DianxinWang/Final-Design/version 2.0/shaft/shaft_side.SLDASM

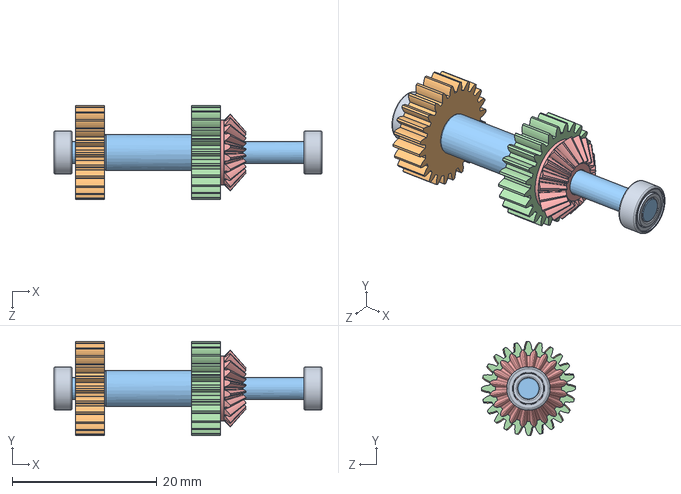
[picture p52: CAD file, 2018-03-30]
version 2.0/shaft/shaft_side.SLDASM
37.0 x 13.0 x 13.0 mm
bearing 3-6-2.5 x 2
shaft_side
