DianxinWang/Final-Design/version 2.0/motor/motor_10_1.SLDASM

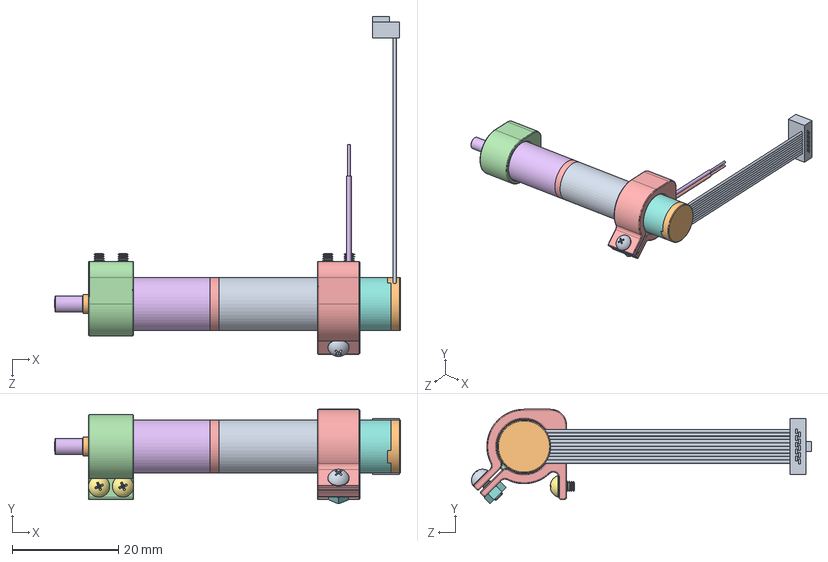
[picture p53: CAD file, 2018-03-30]
version 2.0/motor/motor_10_1.SLDASM
65.1 x 17.8 x 63.9 mm
motor_base-10_11
motor_base-10_22
motor_10_transfer
screw_shi M2X3 x 4
nut M2
screw_shi M2X5
