DianxinWang/Final-Design/version 2.0/shaft/shaft_side_1.SLDASM

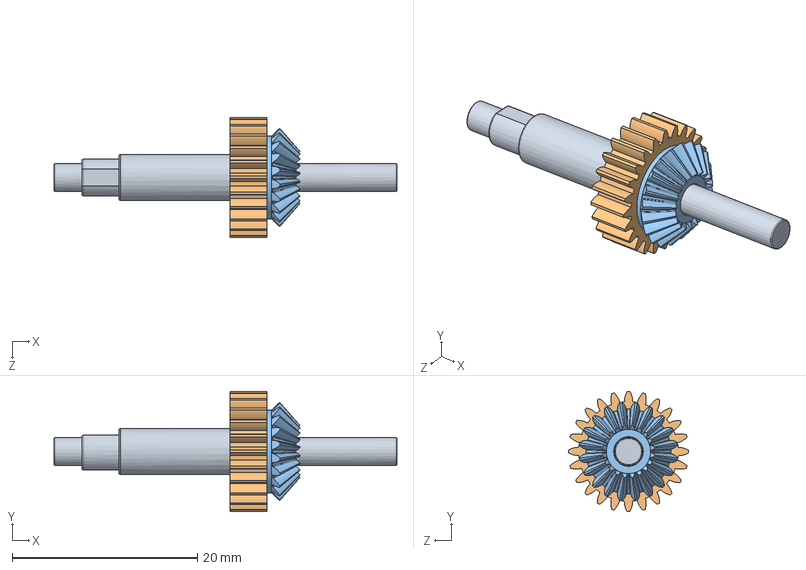
[picture p54: CAD file, 2018-03-30]
version 2.0/shaft/shaft_side_1.SLDASM
37.0 x 13.0 x 13.0 mm
shaft_side
GB - Spur gear 0.5M 24T 20PA 4FW
GB - Straight bevel pinion 0.5M20PT 20GT 20PA 3.3FW
