DianxinWang/Final-Design/version 2.0/motor/motor_10/maxon_dcx10.SLDASM

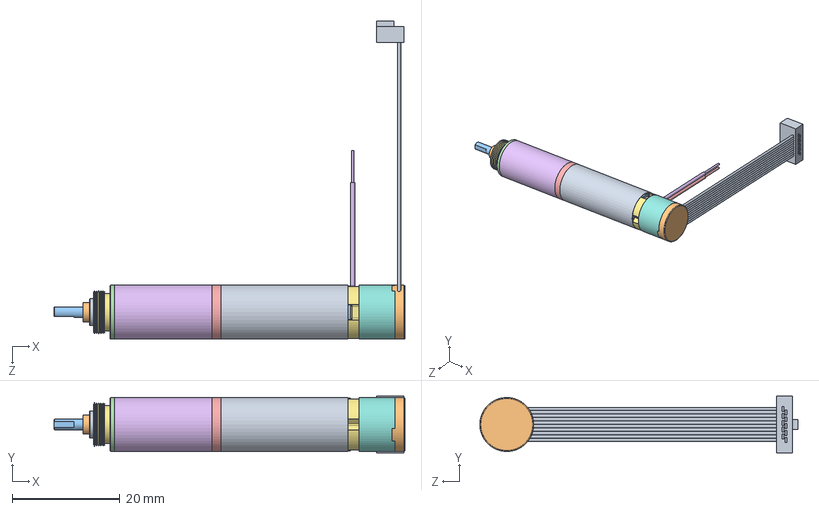
[picture p55: CAD file, 2018-03-30]
version 2.0/motor/motor_10/maxon_dcx10.SLDASM
65.1 x 10.5 x 59.0 mm
