DianxinWang/Final-Design/version 2.0/Index/index-1-1.SLDPRT

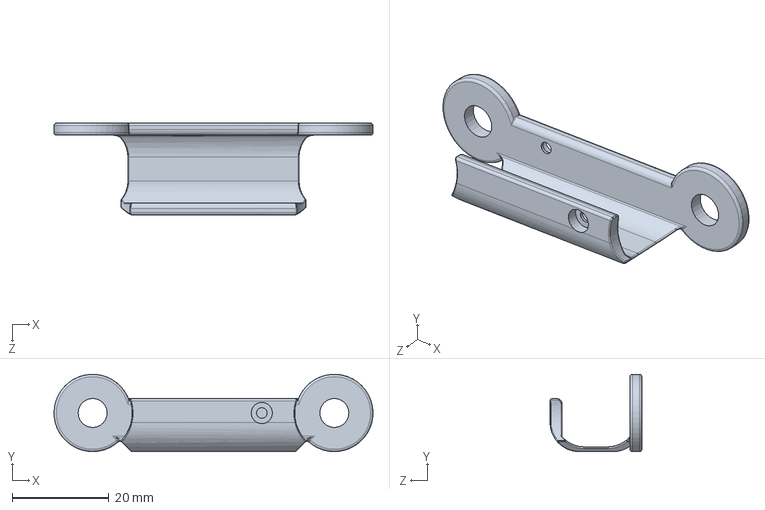
[picture p56: CAD file, 2018-03-30]
version 2.0/Index/index-1-1.SLDPRT
66.0 x 16.0 x 19.0 mm
