DianxinWang/Final-Design/version 2.0/little_finger/little_finger-2.SLDPRT

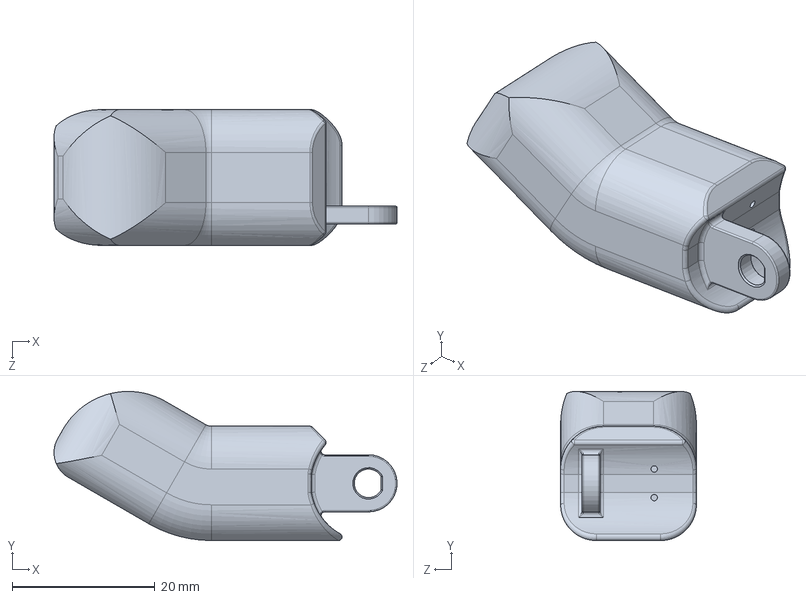
[picture p57: CAD file, 2018-03-30]
version 2.0/little_finger/little_finger-2.SLDPRT
48.0 x 20.9 x 19.0 mm
