DianxinWang/Final-Design/version 2.0/middle_finger/middle_finger-1-2.SLDPRT

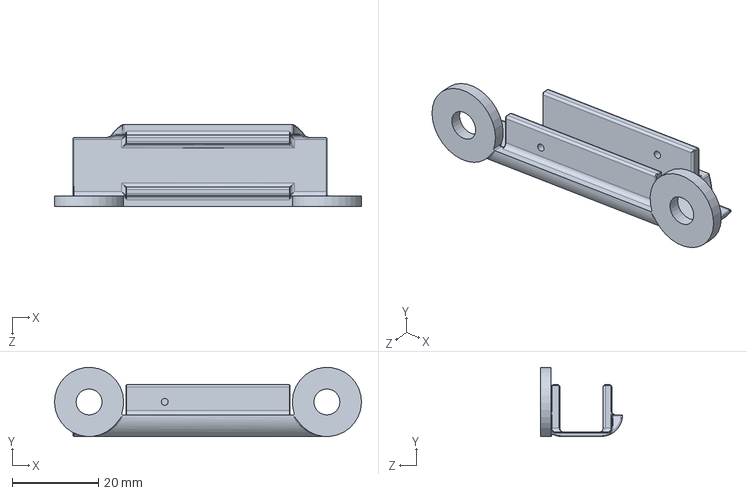
[picture p58: CAD file, 2018-03-30]
version 2.0/middle_finger/middle_finger-1-2.SLDPRT
71.0 x 16.0 x 19.0 mm
