DianxinWang/Final-Design/version 2.0/motor/f-motor-base/motor_base-11.SLDPRT

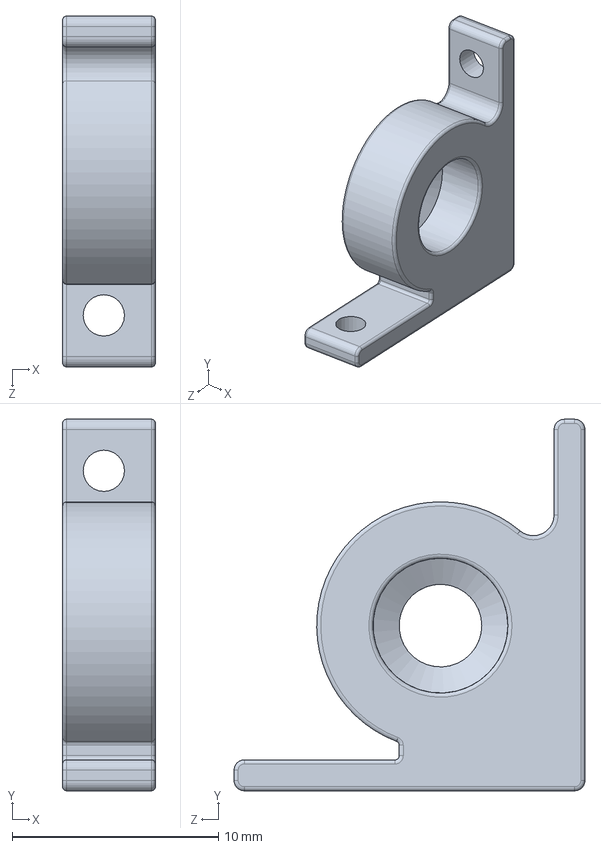
[picture p59: CAD file, 2018-03-30]
version 2.0/motor/f-motor-base/motor_base-11.SLDPRT
4.50 x 18.0 x 17.0 mm
