DianxinWang/Final-Design/version 2.0/motor/motor_10/Gear.sldprt

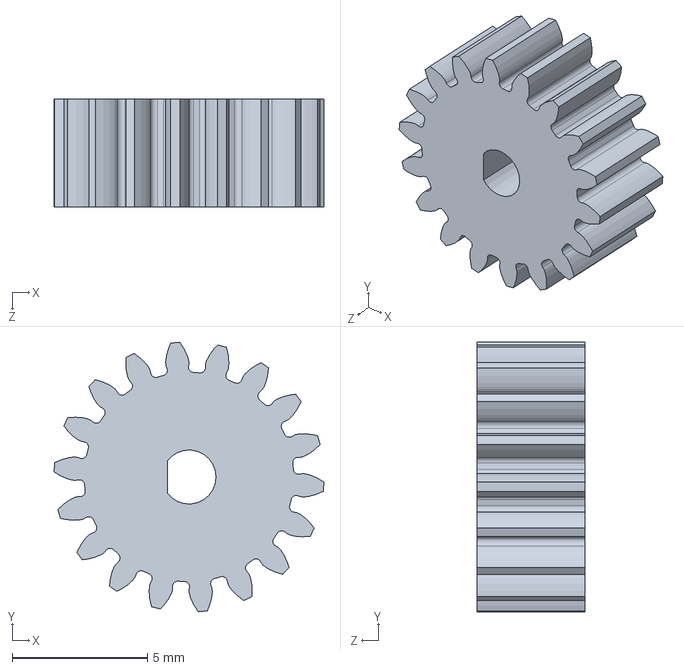
[picture p60: CAD file, 2018-03-30]
version 2.0/motor/motor_10/Gear.sldprt
9.99 x 9.98 x 4.00 mm
