DianxinWang/Final-Design/version 2.0/motor/motor_base-10_2.SLDPRT

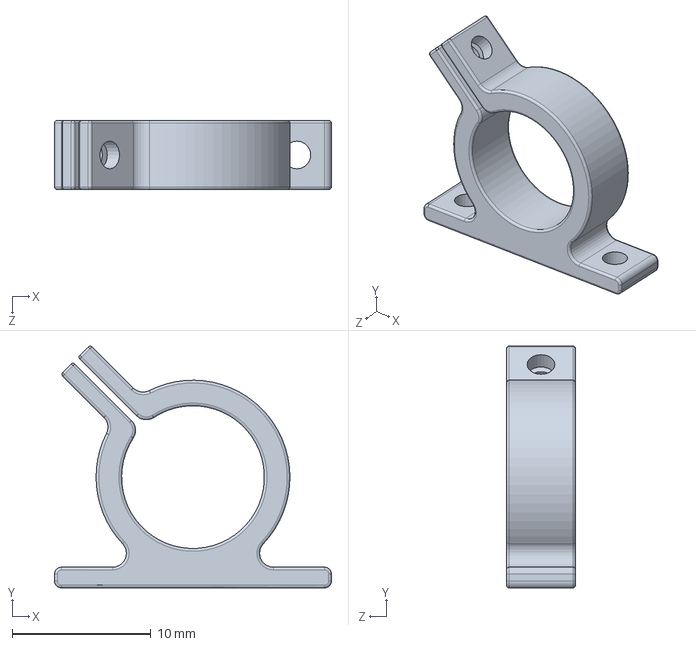
[picture p61: CAD file, 2018-03-30]
version 2.0/motor/motor_base-10_2.SLDPRT
20.0 x 17.5 x 5.00 mm
