DianxinWang/Final-Design/version 2.0/palm/bearing_base_1.SLDPRT

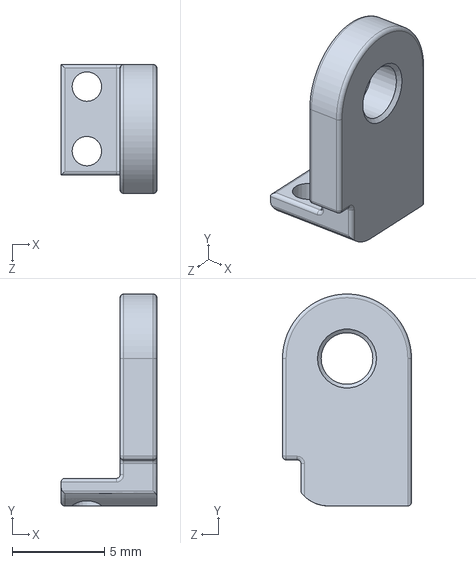
[picture p62: CAD file, 2018-03-30]
version 2.0/palm/bearing_base_1.SLDPRT
5.20 x 11.5 x 7.00 mm
