DianxinWang/Final-Design/version 2.0/传动件图纸/5-gear 0.5M 24T 4FW & pulley 2GT-16 5FW（有修改）.STEP

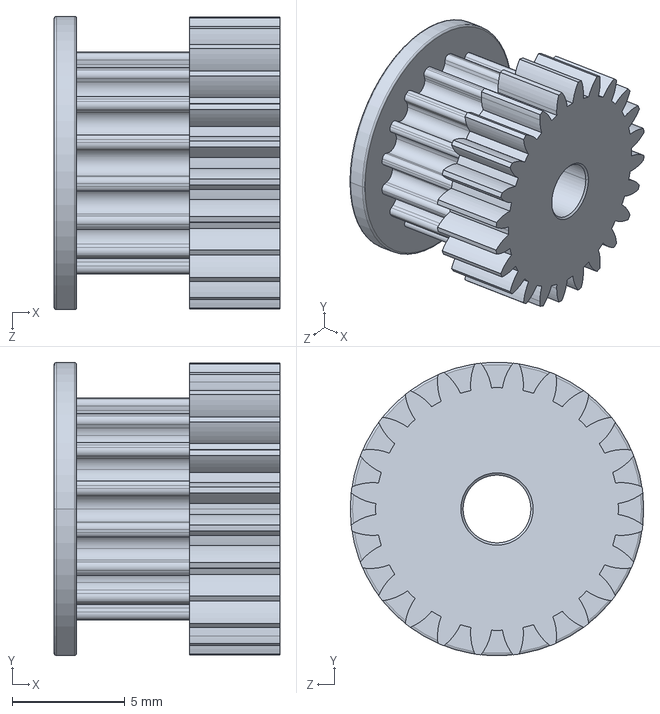
[picture p63: CAD file, 2018-03-30]
version 2.0/传动件图纸/5-gear 0.5M 24T 4FW & pulley 2GT-16 5FW（有修改）.STEP
10.0 x 13.0 x 13.0 mm
