DianxinWang/Final-Design/version 2.0/标准件/bearing 2-5-2.3.sldprt

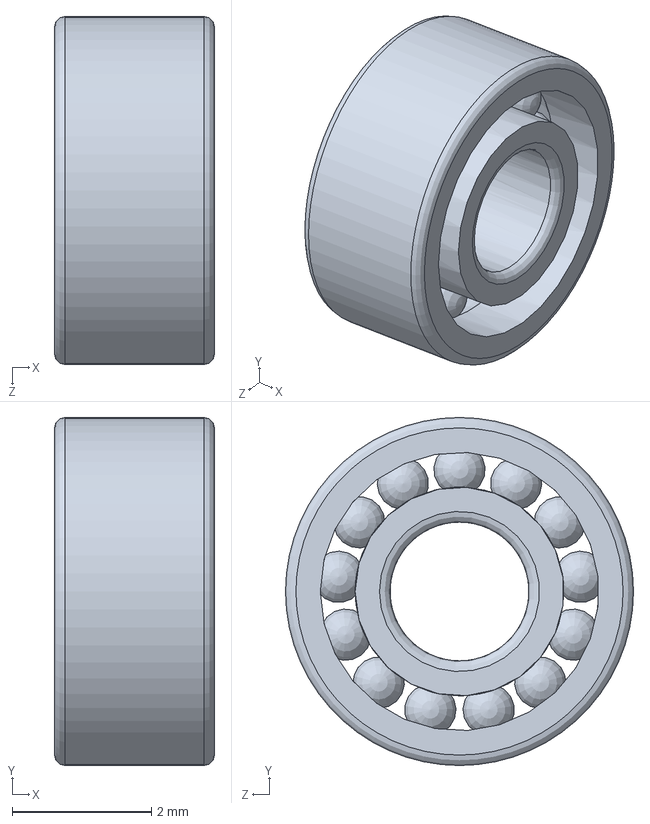
[picture p64: CAD file, 2018-03-30]
version 2.0/标准件/bearing 2-5-2.3.sldprt
2.30 x 5.00 x 5.00 mm
