DianxinWang/Final-Design/version 2.0/标准件/waste/gear 0.5M 24T 4.5FW-pulley 2GT-162.SLDPRT

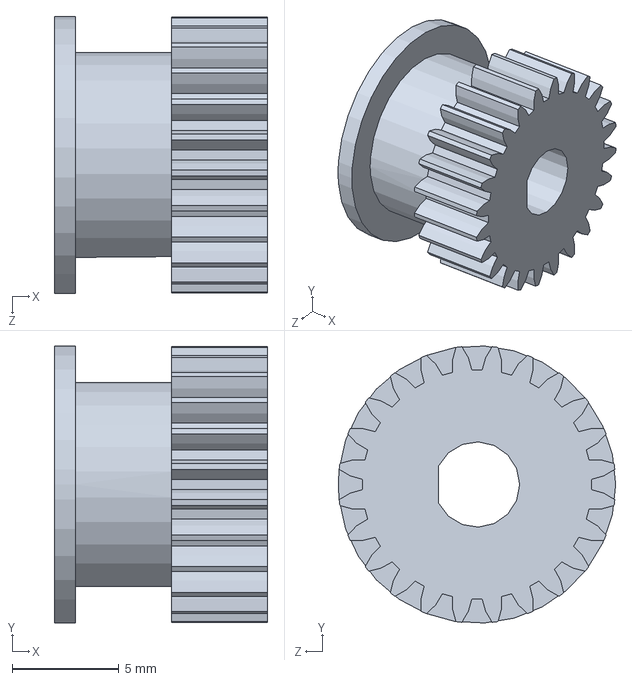
[picture p65: CAD file, 2018-03-30]
version 2.0/标准件/waste/gear 0.5M 24T 4.5FW-pulley 2GT-162.SLDPRT
10.0 x 13.0 x 13.0 mm
