DianxinWang/Final-Design/version 2.0/Index/index-1-2.SLDPRT

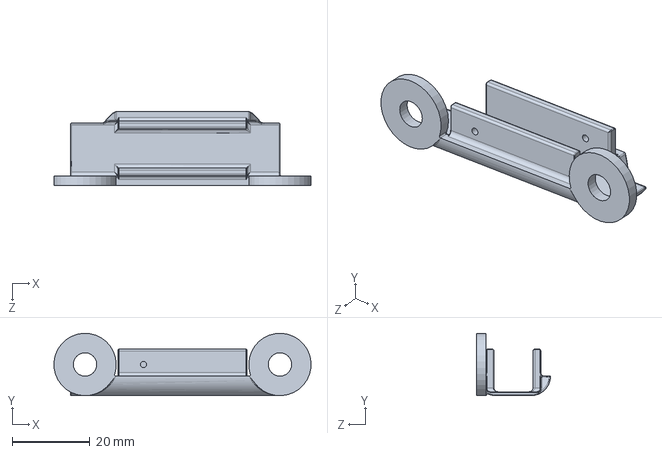
[picture p66: CAD file, 2018-03-30]
version 2.0/Index/index-1-2.SLDPRT
65.9 x 16.0 x 19.0 mm
