DianxinWang/Final-Design/version 2.0/little_finger/little_finger-1-2.SLDPRT

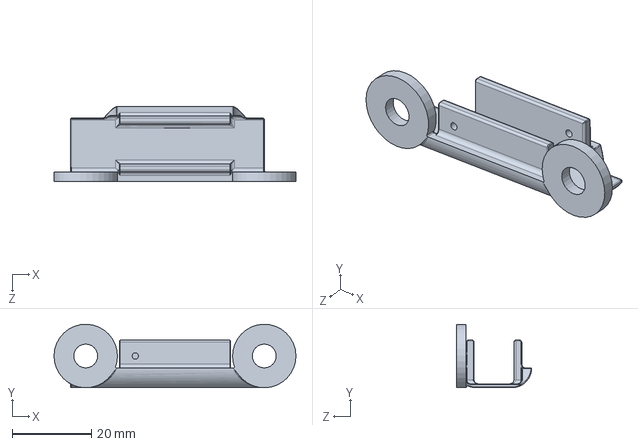
[picture p67: CAD file, 2018-03-30]
version 2.0/little_finger/little_finger-1-2.SLDPRT
61.0 x 16.0 x 19.0 mm
