DianxinWang/Final-Design/version 2.0/middle_finger/middle_finger-2.SLDPRT

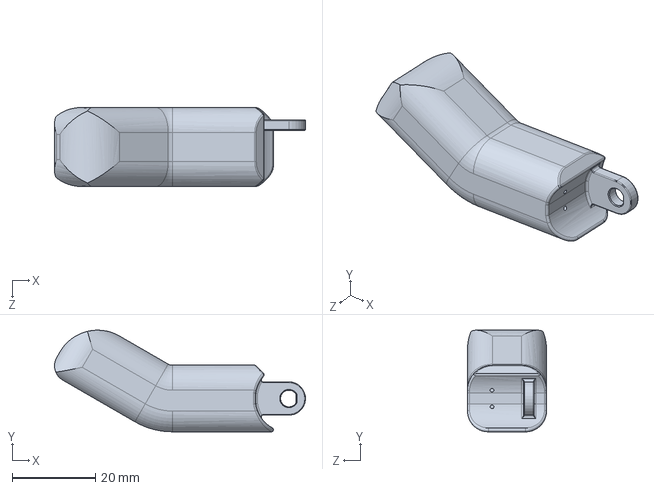
[picture p68: CAD file, 2018-03-30]
version 2.0/middle_finger/middle_finger-2.SLDPRT
60.3 x 24.4 x 19.0 mm
