DianxinWang/Final-Design/version 2.0/motor/f-motor-base/motor_base-22.SLDPRT

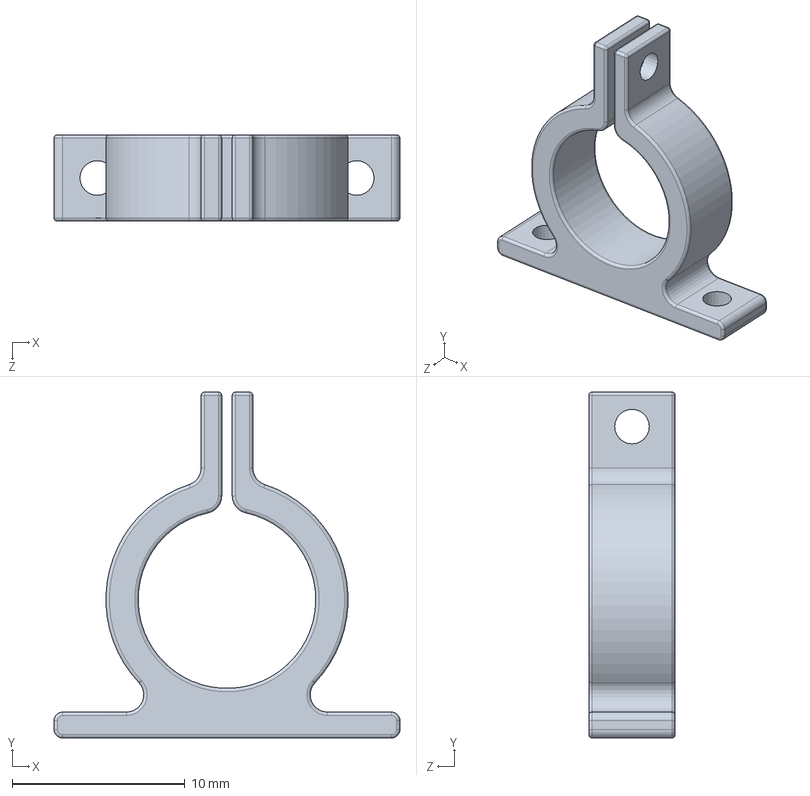
[picture p69: CAD file, 2018-03-30]
version 2.0/motor/f-motor-base/motor_base-22.SLDPRT
20.0 x 20.0 x 5.00 mm
