DianxinWang/Final-Design/version 2.0/motor/motor_16/11.sldprt

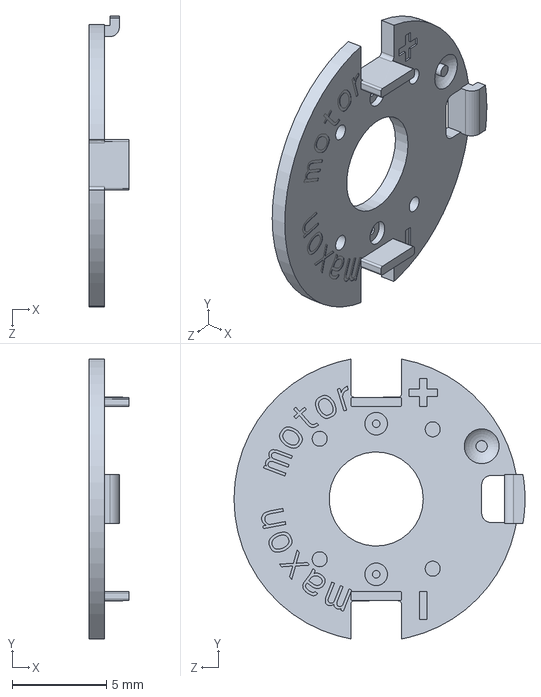
[picture p70: CAD file, 2018-03-30]
version 2.0/motor/motor_16/11.sldprt
2.10 x 14.9 x 15.5 mm
