DianxinWang/Final-Design/version 2.0/motor/motor_base-16_2.SLDPRT

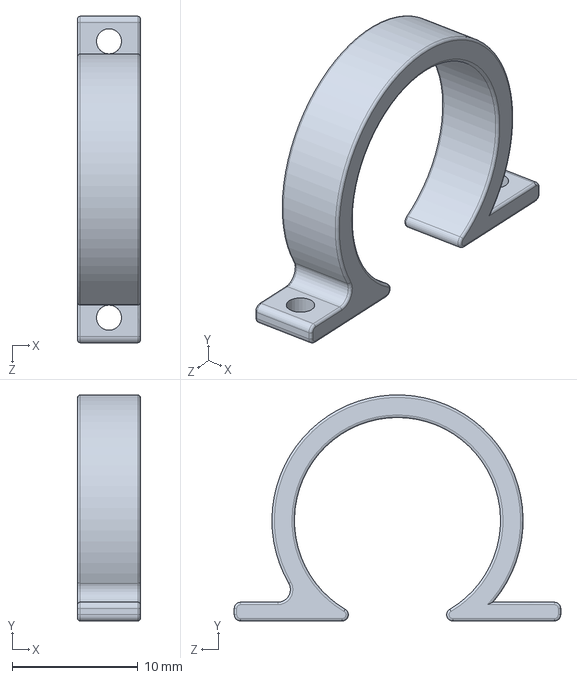
[picture p71: CAD file, 2018-03-30]
version 2.0/motor/motor_base-16_2.SLDPRT
5.00 x 18.0 x 26.0 mm
