DianxinWang/Final-Design/version 2.0/palm/palm-1.SLDPRT

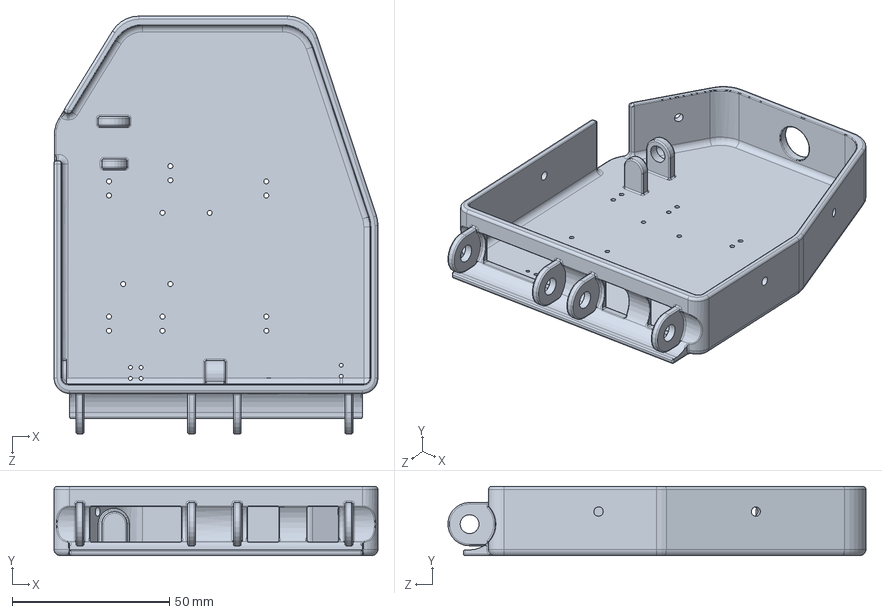
[picture p72: CAD file, 2018-03-30]
version 2.0/palm/palm-1.SLDPRT
103.0 x 22.0 x 132.8 mm
