DianxinWang/Final-Design/version 2.0/ring_finger/ring_finger-2.SLDPRT

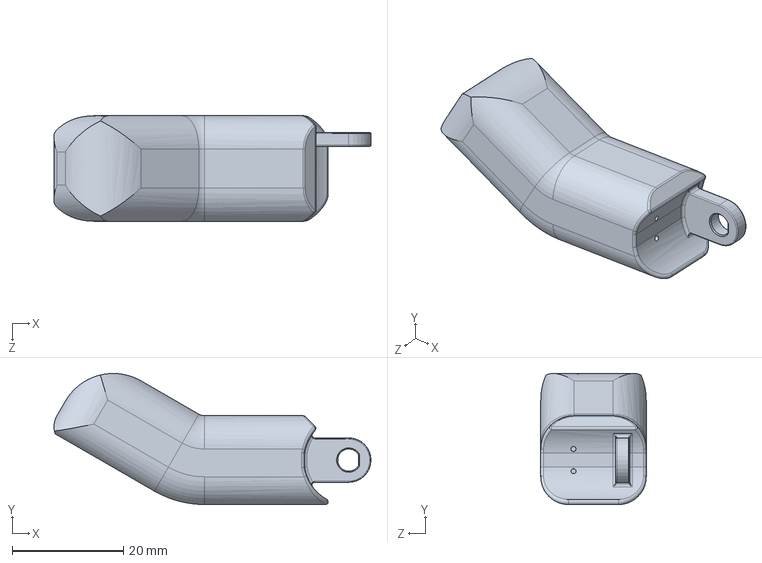
[picture p73: CAD file, 2018-03-30]
version 2.0/ring_finger/ring_finger-2.SLDPRT
57.1 x 23.6 x 19.0 mm
