DianxinWang/Final-Design/version 2.0/传动件图纸/4-gear 0.5M 24T 4FW.STEP

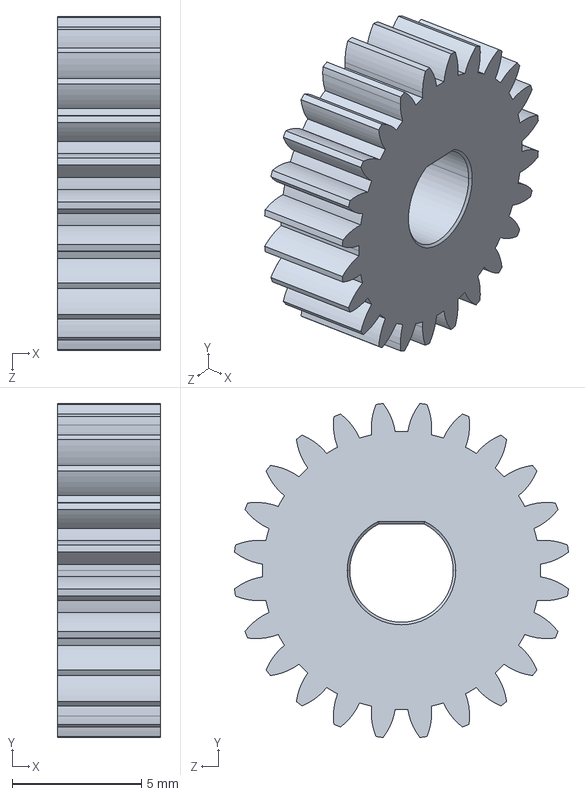
[picture p74: CAD file, 2018-03-30]
version 2.0/传动件图纸/4-gear 0.5M 24T 4FW.STEP
4.00 x 12.9 x 12.9 mm
