DianxinWang/Final-Design/version 2.0/标准件/pulley 2GT-16 4.5FW.SLDPRT

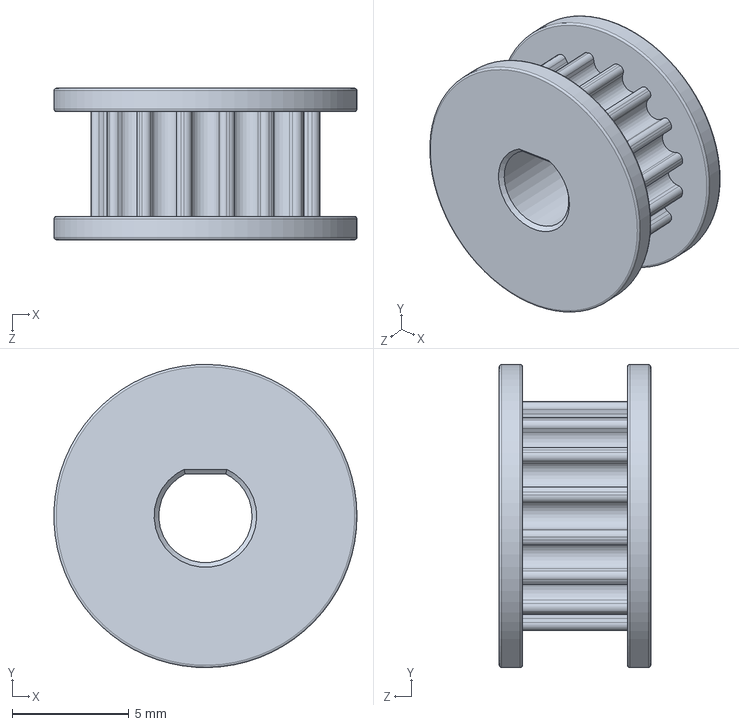
[picture p75: CAD file, 2018-03-30]
version 2.0/标准件/pulley 2GT-16 4.5FW.SLDPRT
13.0 x 13.0 x 6.50 mm
