DianxinWang/Final-Design/version 2.0/标准件/waste/pulley 2GT-16 4.51.SLDPRT

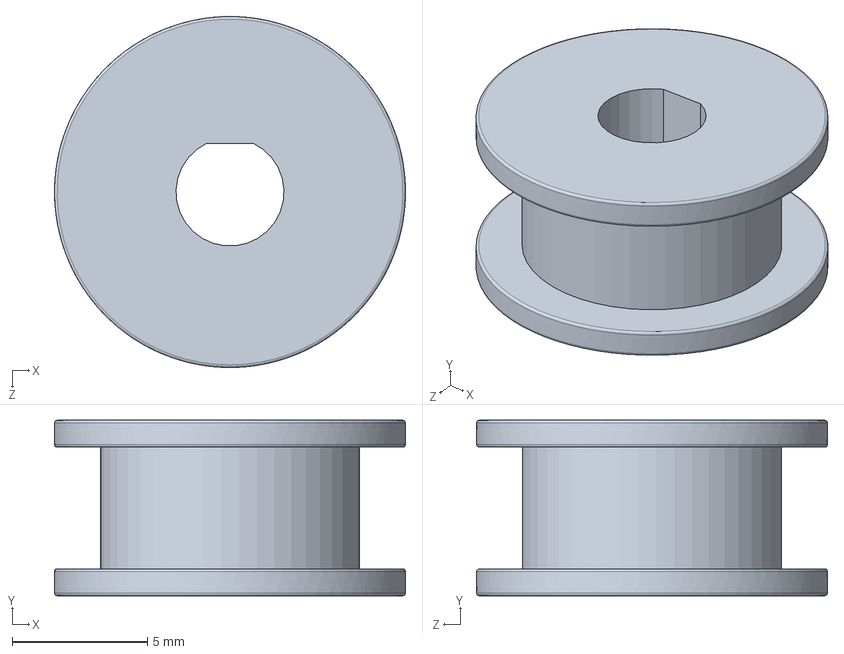
[picture p76: CAD file, 2018-03-30]
version 2.0/标准件/waste/pulley 2GT-16 4.51.SLDPRT
13.0 x 6.50 x 13.0 mm
