DianxinWang/Final-Design/version 2.0/motor/f-motor-base/motor_base-21.SLDPRT

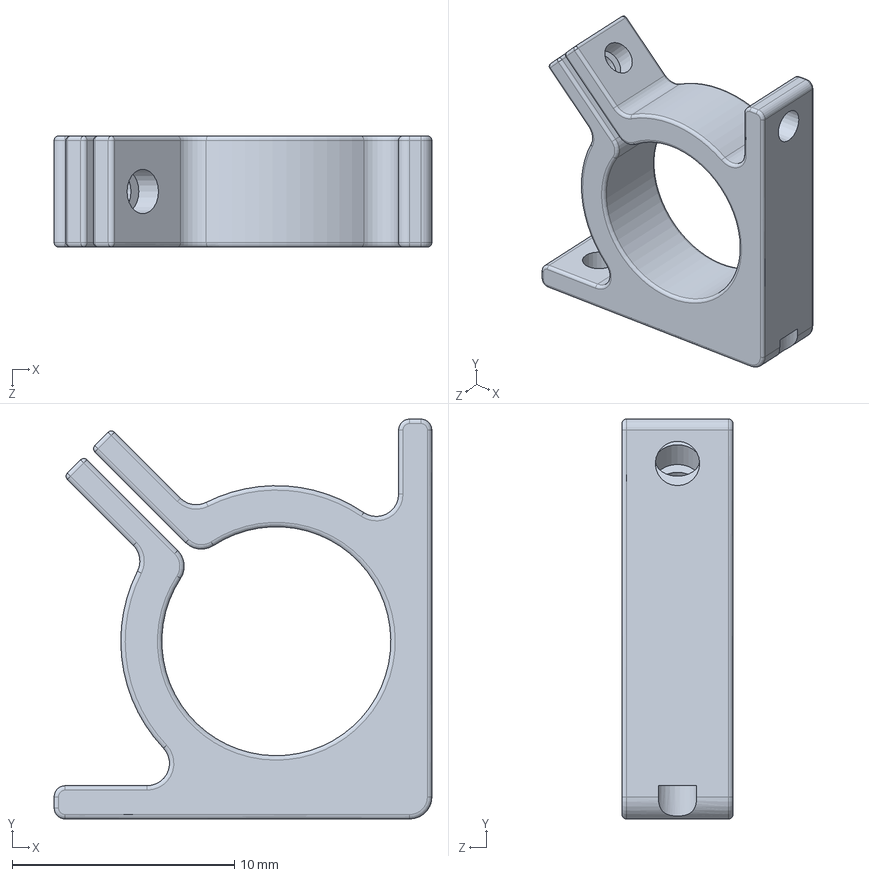
[picture p79: CAD file, 2018-03-30]
version 2.0/motor/f-motor-base/motor_base-21.SLDPRT
17.0 x 18.0 x 5.00 mm
