DianxinWang/Final-Design/version 2.0/palm/palm-2.SLDPRT

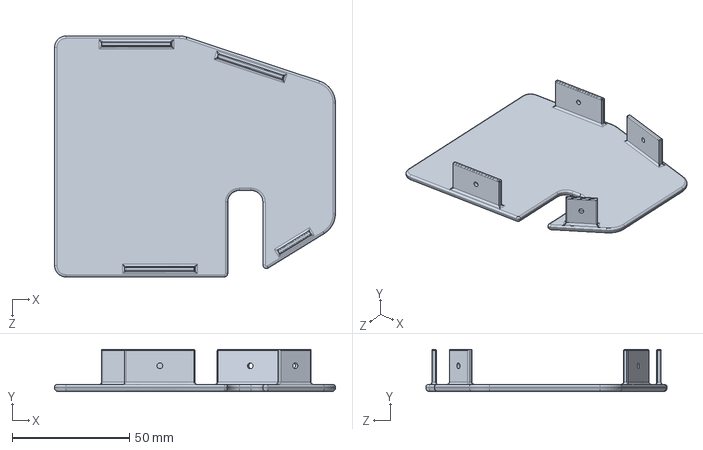
[picture p81: CAD file, 2018-03-30]
version 2.0/palm/palm-2.SLDPRT
120.0 x 18.0 x 103.0 mm
