DianxinWang/Final-Design/version 2.0/thumb/thumb.SLDPRT

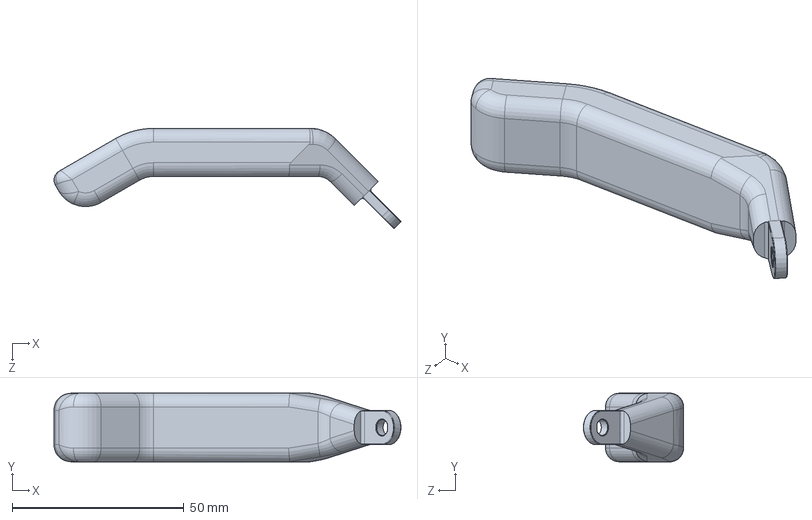
[picture p82: CAD file, 2018-03-30]
version 2.0/thumb/thumb.SLDPRT
101.1 x 20.0 x 29.2 mm
