DianxinWang/Final-Design/version 2.0/标准件/copper_cylinder M2X12+3.SLDPRT

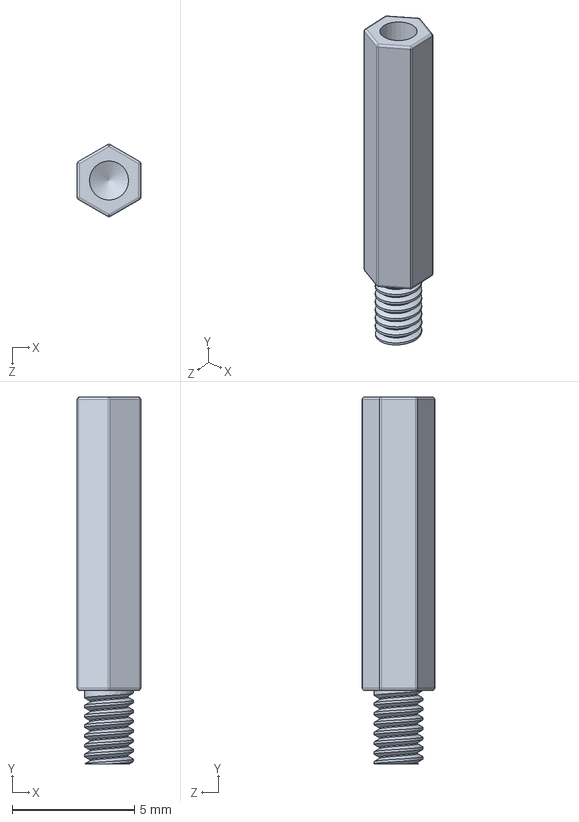
[picture p83: CAD file, 2018-03-30]
version 2.0/标准件/copper_cylinder M2X12+3.SLDPRT
2.60 x 15.0 x 2.97 mm
