DianxinWang/Final-Design/version 2.0/标准件/waste/gear 0.5M30T.SLDPRT

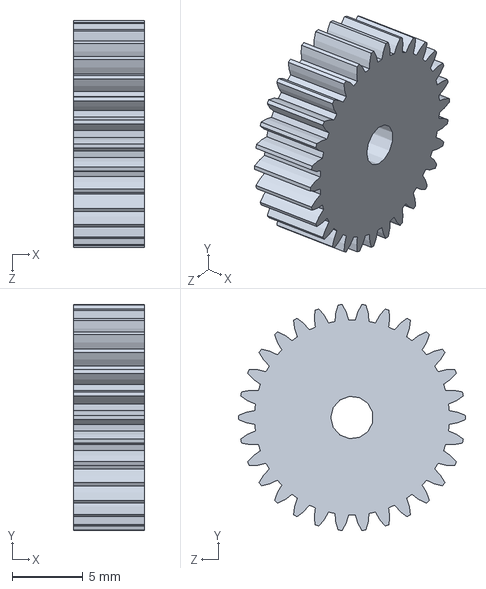
[picture p84: CAD file, 2018-03-30]
version 2.0/标准件/waste/gear 0.5M30T.SLDPRT
5.00 x 15.9 x 16.0 mm
