DianxinWang/Final-Design/version 2.0/Index/2.SLDPRT

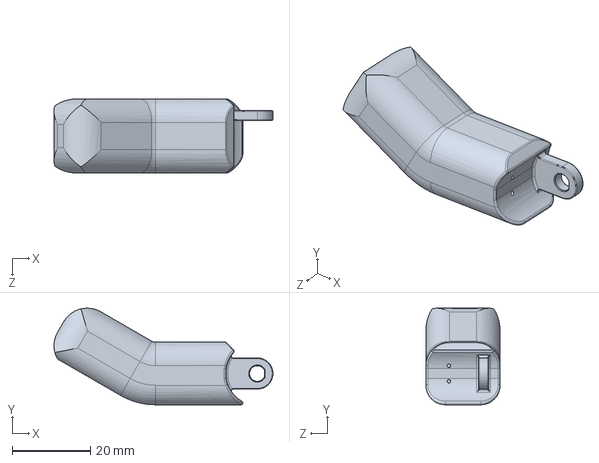
[picture p85: CAD file, 2018-03-30]
version 2.0/Index/2.SLDPRT
56.0 x 24.7 x 19.0 mm
