DianxinWang/Final-Design/version 2.0/传动件图纸/1-bevel gear.STEP

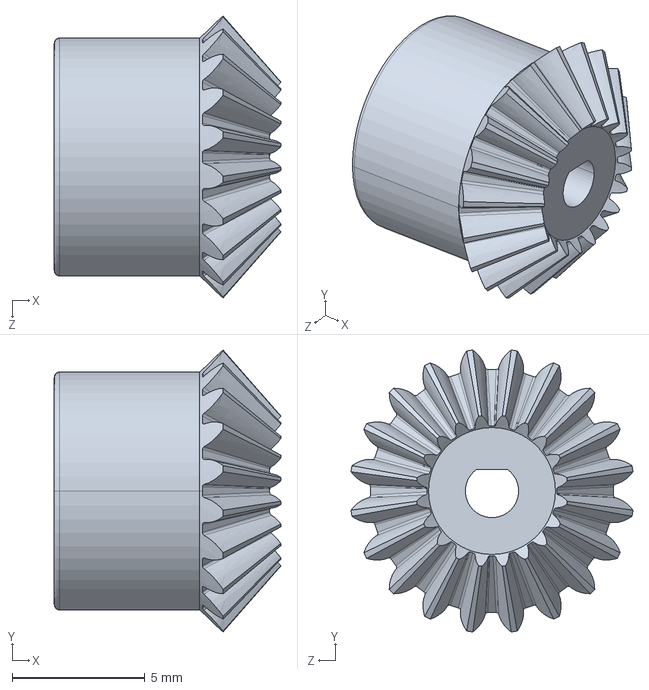
[picture p86: CAD file, 2018-03-30]
version 2.0/传动件图纸/1-bevel gear.STEP
8.52 x 10.6 x 10.6 mm
