DianxinWang/Final-Design/version 2.0/标准件/bearing 3-6-2.5.sldprt

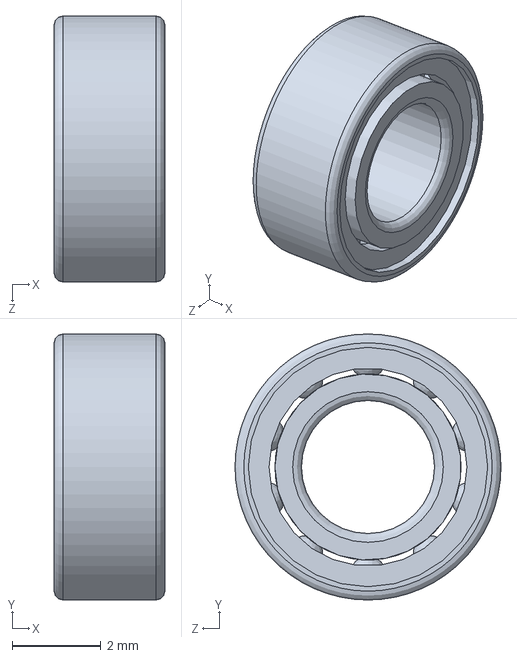
[picture p87: CAD file, 2018-03-30]
version 2.0/标准件/bearing 3-6-2.5.sldprt
2.50 x 6.00 x 6.00 mm
