DianxinWang/Final-Design/version 2.0/motor/motor_16/16.sldprt

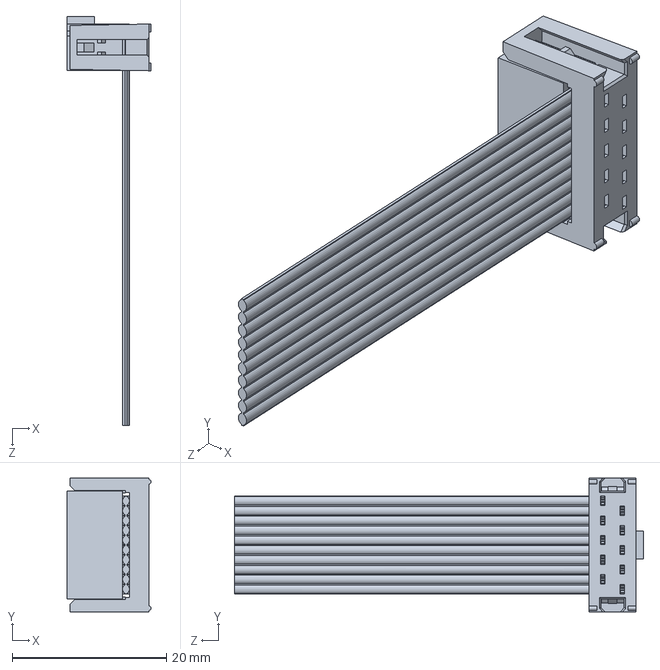
[picture p88: CAD file, 2018-03-30]
version 2.0/motor/motor_16/16.sldprt
10.9 x 17.3 x 52.9 mm
