DianxinWang/Final-Design/version 2.0/motor/motor_base-16_1.SLDPRT

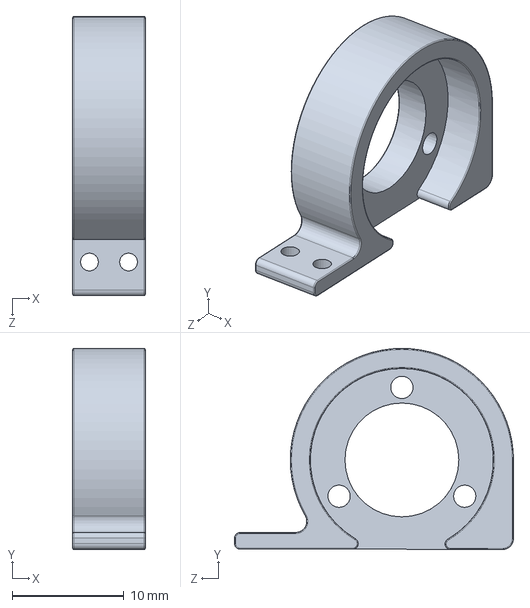
[picture p89: CAD file, 2018-03-30]
version 2.0/motor/motor_base-16_1.SLDPRT
6.50 x 18.0 x 25.0 mm
