DianxinWang/Final-Design/version 2.0/palm/bearing_base_2.SLDPRT

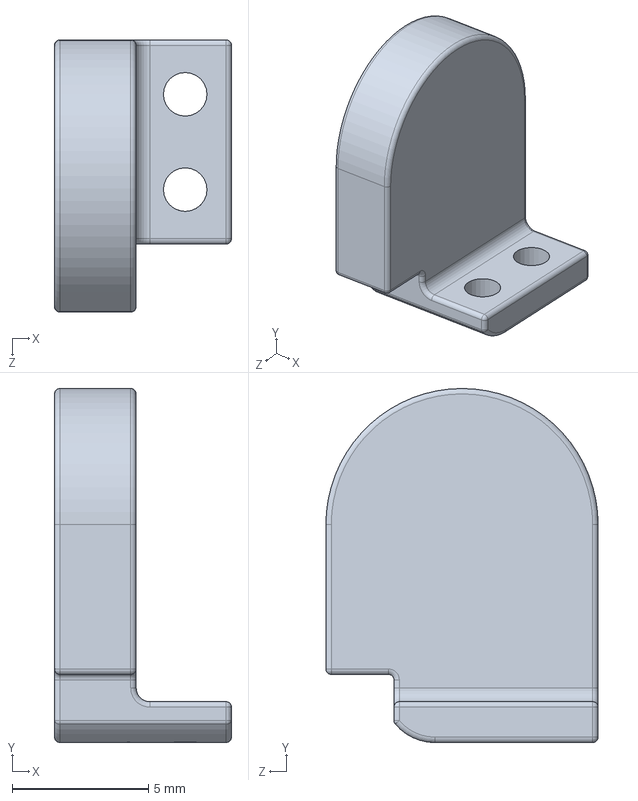
[picture p90: CAD file, 2018-03-30]
version 2.0/palm/bearing_base_2.SLDPRT
6.50 x 13.0 x 10.0 mm
