DianxinWang/Final-Design/version 2.0/motor/motor_base-10_22.SLDPRT

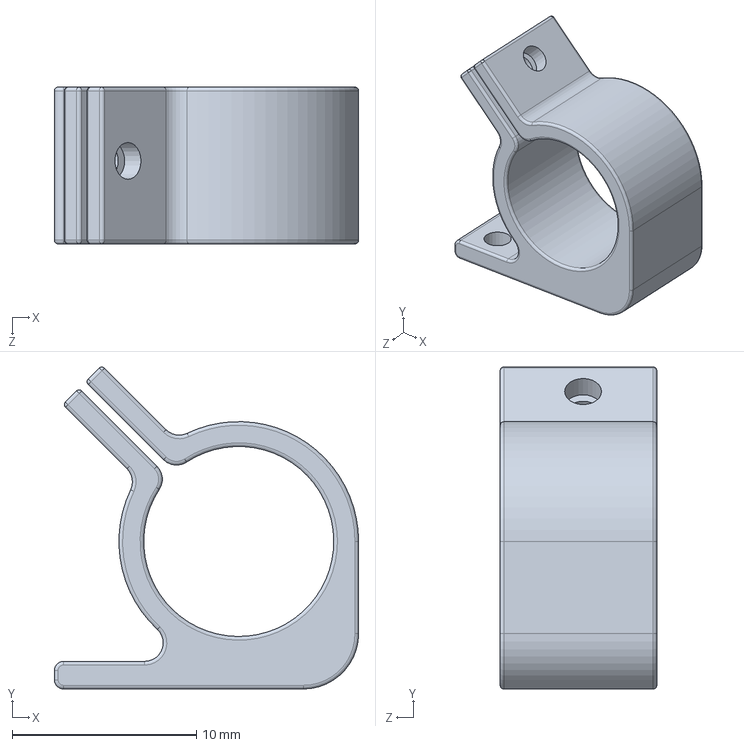
[picture p91: CAD file, 2018-03-30]
version 2.0/motor/motor_base-10_22.SLDPRT
16.5 x 17.5 x 8.50 mm
