DianxinWang/Final-Design/version 2.0/标准件/waste/gear 0.5M 24T 4.5FW-bevel gear 0.5M 20T.STEP

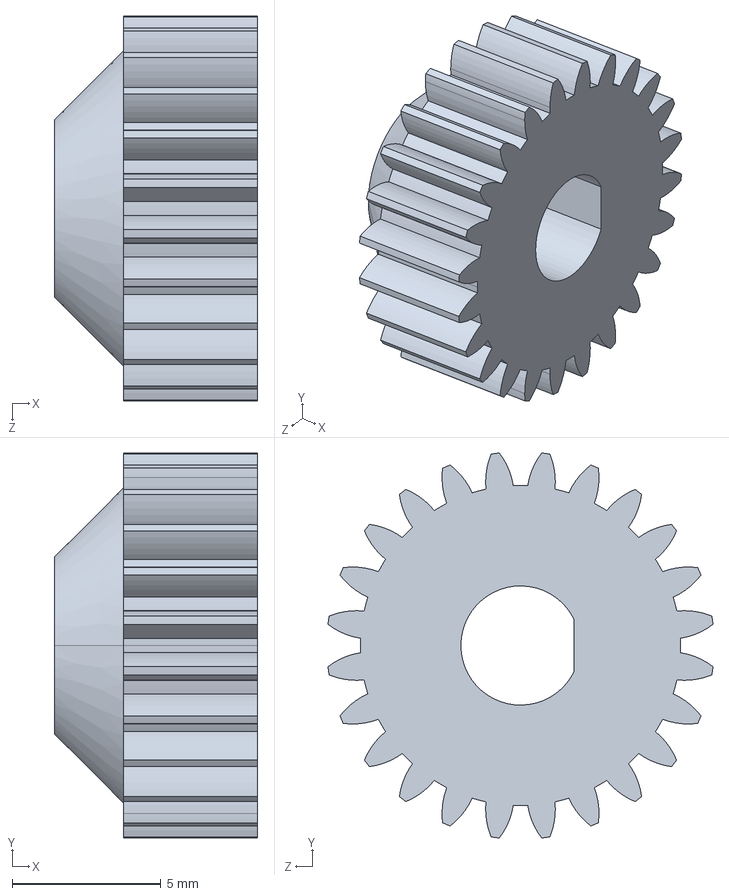
[picture p93: CAD file, 2018-03-30]
version 2.0/标准件/waste/gear 0.5M 24T 4.5FW-bevel gear 0.5M 20T.STEP
6.83 x 12.9 x 12.9 mm
