DianxinWang/Final-Design/version 2.0/motor/motor_10_transfer.SLDPRT

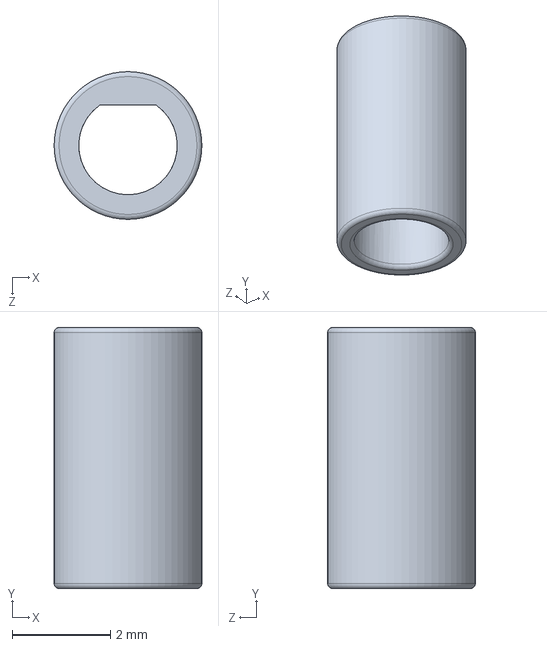
[picture p94: CAD file, 2018-03-30]
version 2.0/motor/motor_10_transfer.SLDPRT
3.00 x 5.30 x 3.00 mm
