DianxinWang/Final-Design/version 2.0/motor/motor_16/14.sldprt

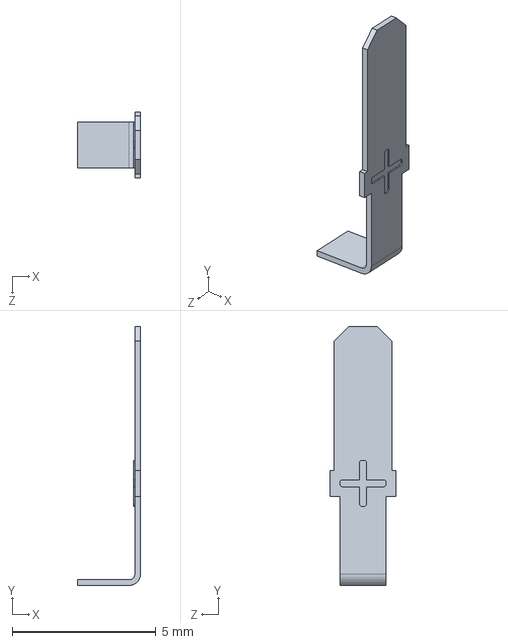
[picture p95: CAD file, 2018-03-30]
version 2.0/motor/motor_16/14.sldprt
2.20 x 9.00 x 2.30 mm
