DianxinWang/Final-Design/version 2.0/shaft/GB - Straight bevel pinion 0.5M20PT 20GT 20PA 3.3FW.SLDPRT

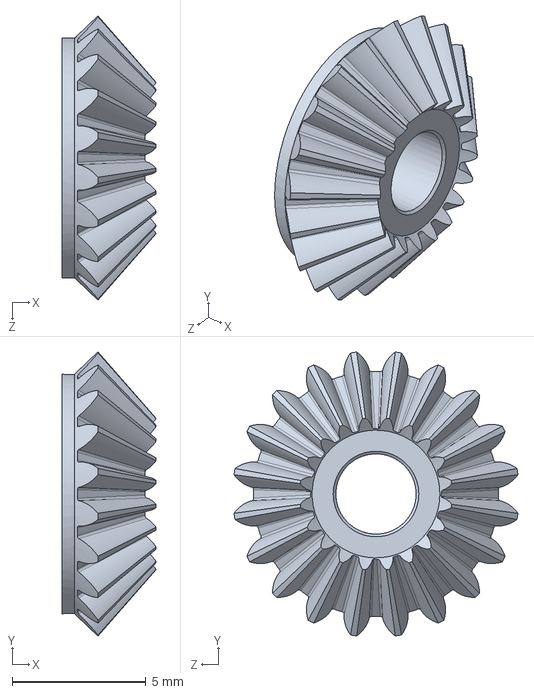
[picture p96: CAD file, 2018-03-30]
version 2.0/shaft/GB - Straight bevel pinion 0.5M20PT 20GT 20PA 3.3FW.SLDPRT
3.52 x 10.6 x 10.6 mm
