DianxinWang/Final-Design/version 2.0/标准件/waste/gear_4.SLDPRT

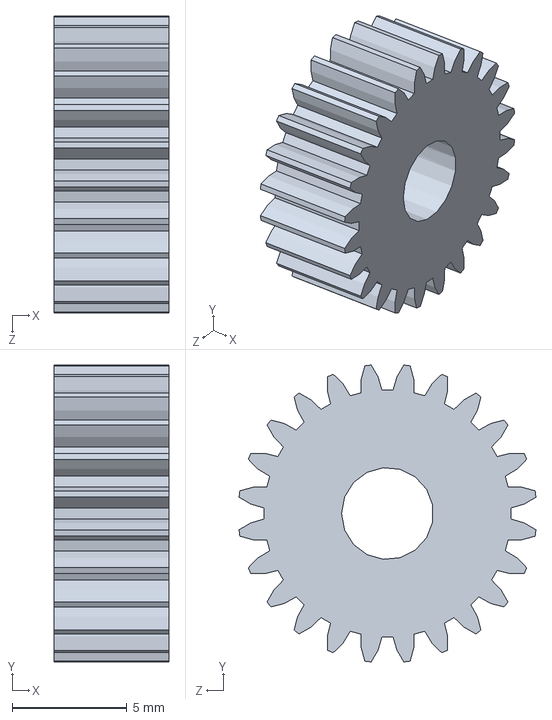
[picture p97: CAD file, 2018-03-30]
version 2.0/标准件/waste/gear_4.SLDPRT
5.00 x 12.9 x 12.9 mm
