DianxinWang/Final-Design/version 2.0/motor/motor_base-10_1.SLDPRT

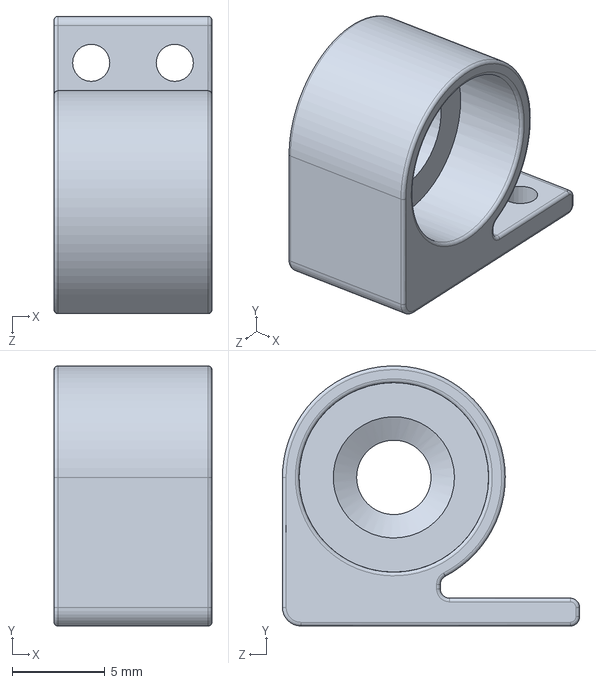
[picture p98: CAD file, 2018-03-30]
version 2.0/motor/motor_base-10_1.SLDPRT
8.50 x 14.0 x 16.0 mm
