DianxinWang/Final-Design/version 2.0/标准件/bevel gear-original.SLDPRT

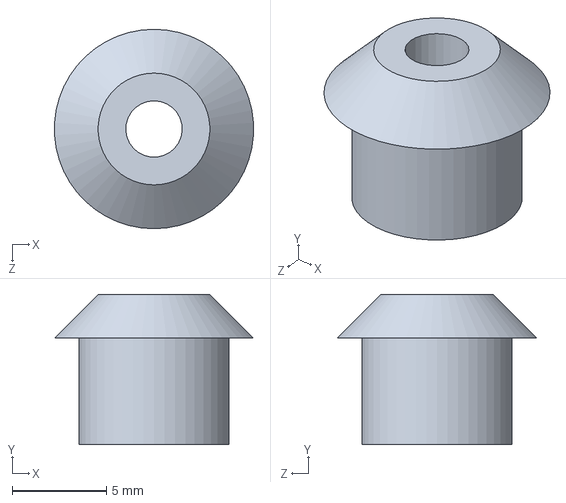
[picture p99: CAD file, 2018-03-30]
version 2.0/标准件/bevel gear-original.SLDPRT
10.6 x 8.00 x 10.6 mm
