DianxinWang/Final-Design/version 2.0/motor/motor_16/12.sldprt

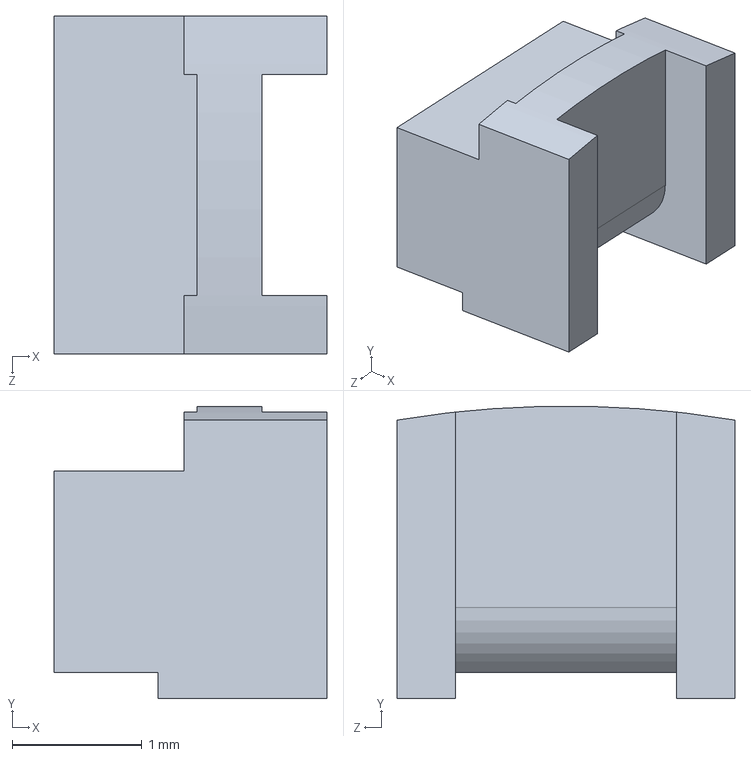
[picture p100: CAD file, 2018-03-30]
version 2.0/motor/motor_16/12.sldprt
2.10 x 2.25 x 2.60 mm
