DianxinWang/Final-Design/version 2.0/标准件/E-clip-2.5.SLDPRT

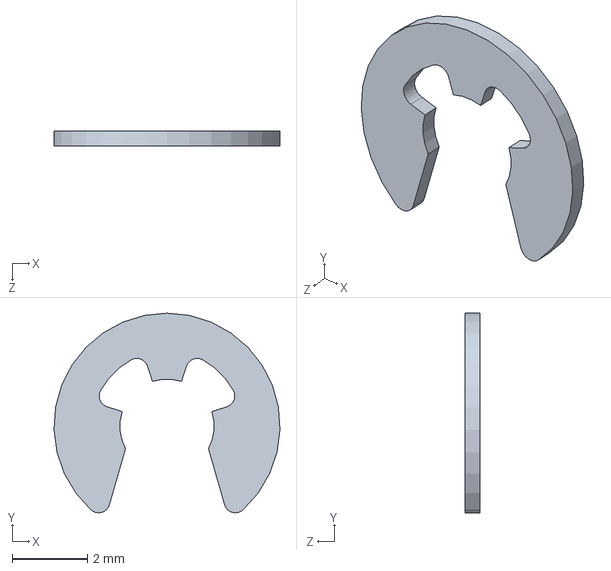
[picture p101: CAD file, 2018-03-30]
version 2.0/标准件/E-clip-2.5.SLDPRT
6.00 x 5.30 x 0.4 mm
