DianxinWang/Final-Design/version 2.0/标准件/bearing 4-7-3.sldprt

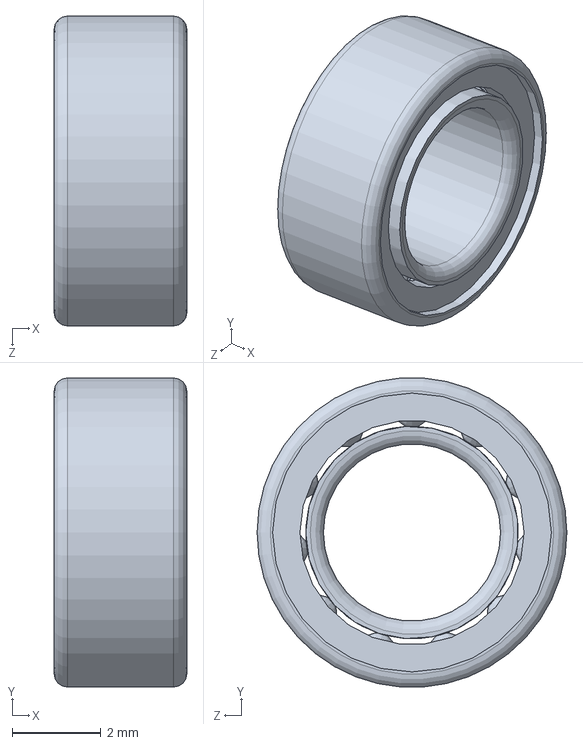
[picture p102: CAD file, 2018-03-30]
version 2.0/标准件/bearing 4-7-3.sldprt
3.00 x 6.98 x 7.00 mm
