DianxinWang/Final-Design/robothand/Src/pid.c

#include <stdlib.h>
#include <math.h>
#include "pid.h"


void pid_init(pid_ctrl_t *pid)
{
    pid_set_gains(pid, 0.022, 0.07, 0.002);
    pid->integrator = 0.;
    pid->previous_error = 0.;
    pid->integrator_limit = INFINITY;
    pid->frequency = 100.;
}

void pid_set_gains(pid_ctrl_t *pid, float kp, float ki, float kd)
{
    pid->kp = kp;
    pid->ki = ki;
    pid->kd = kd;
}

void pid_get_gains(const pid_ctrl_t *pid, float *kp, float *ki, float *kd)
{
    *kp = pid->kp;
    *ki = pid->ki;
    *kd = pid->kd;
}

float pid_get_integral_limit(const pid_ctrl_t *pid)
{
    return pid->integrator_limit;
}

float pid_get_integral(const pid_ctrl_t *pid)
{
    return pid->integrator;
}

float pid_process(pid_ctrl_t *pid, float error)
{
    float output;
    pid->integrator += error;

    if (pid->integrator > pid->integrator_limit) {
        pid->integrator = pid->integrator_limit;
    } else if (pid->integrator < -pid->integrator_limit) {
        pid->integrator = -pid->integrator_limit;
    }

    output  = - pid->kp * error;
    output += - pid->ki * pid->integrator / pid->frequency;
    output += - pid->kd * (error - pid->previous_error) * pid->frequency;

    pid->previous_error = error;
		if(error > 700){
			output = -100;
			pid->integrator=0;
		}
		else if(error < -700){
			output = 100;
			pid->integrator=0;
		}
    return output;
}

void pid_set_integral_limit(pid_ctrl_t *pid, float max)
{
    pid->integrator_limit = max;
}

void pid_reset_integral(pid_ctrl_t *pid)
{
    pid->integrator = 0.;
}

void pid_set_frequency(pid_ctrl_t *pid, float frequency)
{
    pid->frequency = frequency;
}

float pid_get_frequency(const pid_ctrl_t *pid)
{
    return pid->frequency;
}
